jsyk/PIP-Watch/doc/gde021a1_framebuffer.png

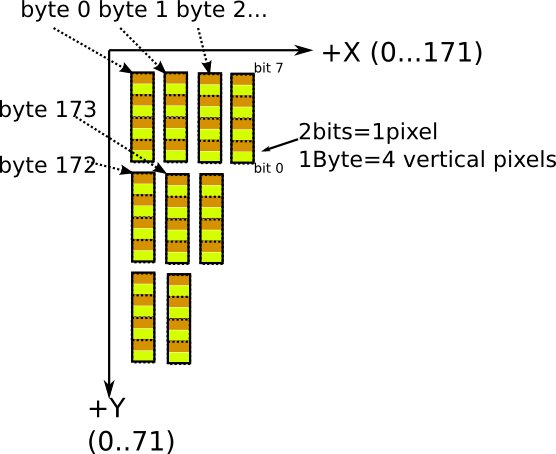
doc/gde021a1_framebuffer.png
