jsyk/PIP-Watch/doc/swarch-whitebg.png

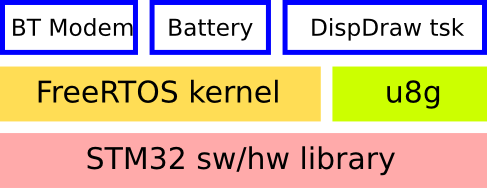
doc/swarch-whitebg.png
