jsyk/PIP-Watch/epd_driver_basic_stm32f101_sw/cube/stm32f101c8t6.jpg

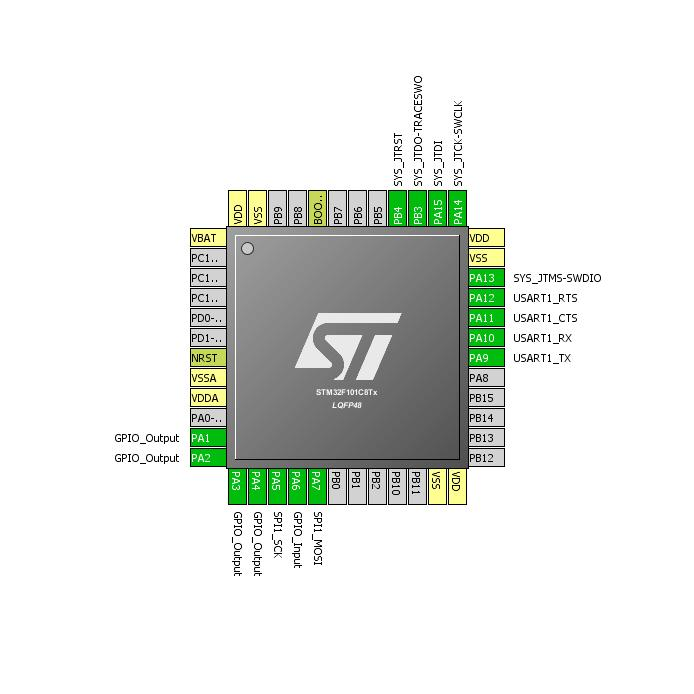
epd_driver_basic_stm32f101_sw/cube/stm32f101c8t6.jpg
