jsyk/PIP-Watch/pipwatch_zero-fw/stm_epd_connection.png

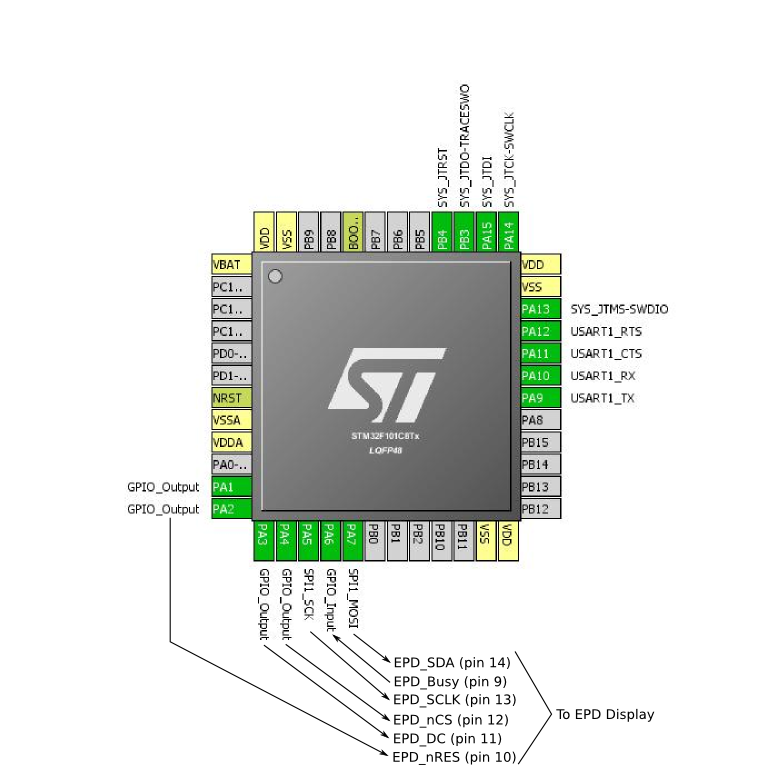
pipwatch_zero-fw/stm_epd_connection.png
