jsyk/PIP-Watch/epd_driver_basic_stm32f101_sw/cube/stm32f101c8t6.ioc

Mcu.UserName=STM32F101C8Tx
PA1.Signal=GPIO_Output
PA10.Signal=USART1_RX
PA11.Signal=USART1_CTS
PA12.Signal=USART1_RTS
PA13.Signal=SYS_JTMS-SWDIO
PA14.Signal=SYS_JTCK-SWCLK
PA15.Signal=SYS_JTDI
PA2.Signal=GPIO_Output
PA3.Signal=GPIO_Output
PA4.Signal=GPIO_Output
PA5.Signal=SPI1_SCK
PA6.Signal=GPIO_Input
PA7.Signal=SPI1_MOSI
PA9.Signal=USART1_TX
PB3.Signal=SYS_JTDO-TRACESWO
PB4.Signal=SYS_JTRST
