jsyk/PIP-Watch/pipwatch_zero-fw/btm.c

#include "btm.h"
#include "main.h"
#include "utils.h"
#include "leds.h"
#include "motor.h"
#include "gui.h"
#include "streamlnk.h"

#include <string.h>
#include <ctype.h>

/* Scheduler includes. */
// #include "FreeRTOS.h"
#include "task.h"
// #include "queue.h"
#include "STM32_USART.h"

/* Library includes. */
#include "stm32f10x_it.h"


/* the state of the bluetooth modem */
int btm_state = BTMST_NonConfigured;



/* Remove all characters already received in USART queue */
void usartDrainInput(long lPort)
{
    int ch;
    while (xSerialGetChar(lPort, &ch, 0) == pdPASS)
        ;
}


/* Receive all characters until the buffer is full or there are none more
 * within the timeout */
int usartGetString(long lPort, char *buf, int buflen, TickType_t xBlockTime)
{
    int ch;            /* current character */
    int cnt = 0;        /* number of chars received */

    while (cnt < (buflen-1)) {
        if (xSerialGetChar(lPort, &ch, xBlockTime) != pdPASS) {
            /* no more chars in the buffer and we waited a timeout -> bail out */
            break;
        }

        /* save the character into buffer */
        buf[cnt++] = ch;
    }

    /* null-terminate, if possible */
    if (cnt < buflen) {
        buf[cnt] = 0;
    }

    /* print the received string to display */
    printstr(buf);

    return cnt;
}

/* Receive characters until the buffer is full or end of line or there are none more
 * within the timeout. */
int usartGetLine(long lPort, char *buf, int buflen, TickType_t xBlockTime)
{
    int ch;            /* current character */
    int cnt = 0;        /* number of chars received */
    int expect_newline = 0;

    while (cnt < (buflen-1)) {
        if (xSerialPeekChar(lPort, &ch, xBlockTime) != pdPASS) {
            /* no more chars in the buffer and we waited a timeout -> bail out */
            break;
        }

        if (expect_newline && ch != '\n') {
            /* we were expecting \n now, but it has not come -> leave ch in the queue and exit */
            break;
        }

        /* save the character into buffer */
        buf[cnt++] = ch;

        /* if it is \r, then expect \n as the next character */
        if (ch == '\r') {
            expect_newline = 1;
        }

        /* physically remove the character we've peeked from the queue */
        xSerialGetChar(lPort, &ch, xBlockTime);

        if (ch == '\n') {
            /* end of line -> end of str, for now */
            break;
        }
    }

    /* null-terminate, if possible */
    if (cnt < buflen) {
        buf[cnt] = 0;
    }

    /* print the received string to display */
    // printstr(buf);

    return cnt;
}


/* Expecting the 'OK' response from modem. Wait for it and do anything
 * possible to decode it. */
int btmExpectOK()
{
    const int buflen = 64;
    char xbuf[buflen];
    int len;

    len = usartGetString(comBTM, xbuf, buflen, ( TickType_t ) 200 / portTICK_PERIOD_MS);

    char *buf = xbuf;

    if (len < 4) {
        goto err;
    }

    if ((buf[0] == 'A' && buf[1] == 'T') || (buf[0] == '\r')) {
        // discard echo text
        while (!(buf[0] == '\r' && buf[1] == '\n')) {
            if (buf[0] == 0) {
                goto err;
            }
            ++buf;
        }
        // skip \r\n
        buf += 2;
    }

    if (buf[0] != 'O') {
        goto err;
    }
    if (buf[1] != 'K') {
        goto err;
    }
    if (buf[2] != '\r') {
        goto err;
    }
    if (buf[3] != '\n') {
        goto err;
    }

    return 0;

err:
#if 0
    zbuf = pvPortMalloc(sizeof(char) * 64);
    strncpy(zbuf, xbuf, len);
    for (int i = 0; i < 63; ++i) {
        if (zbuf[i] == '\r' || zbuf[i] == '\n') {
            zbuf[i] = ' ';
        }
    }
    zbuf[63] = 0;
    xQueueSend(toDisplayStrQueue, &zbuf, 0);
#endif
    return 1;
}

void setBtmState(int new_btmst)
{
    btm_state = new_btmst;

    switch (btm_state) {
        case BTMST_NonConfigured:
            LEDs_Set(LED0, LED_INTENS_100, LED_INTENS_0, LED_INTENS_0);
            break;

        case BTMST_Configured:
            LEDs_Set(LED0, LED_INTENS_100, LED_INTENS_100, LED_INTENS_0);
            break;

        case BTMST_Listening:
            LEDs_Set(LED0, LED_INTENS_0, LED_INTENS_100, LED_INTENS_0);
            break;

        case BTMST_Connected:
            LEDs_Set(LED0, LED_INTENS_0, LED_INTENS_0, LED_INTENS_100);
            break;

        default: break;
    }
}


void btmInitModem()
{
    /* Initialise COM0, which is USART1 according to the STM32 libraries. */
    lCOMPortInit( comBTM, mainBAUD_RATE );

    setBtmState(BTMST_NonConfigured);

    /* Reset BTM */
    #if 0
    GPIO_ResetBits(BTM_Reset_Port, BTM_Reset_Pin);
    vTaskDelay( ( TickType_t ) 10 / portTICK_PERIOD_MS );
    GPIO_SetBits(BTM_Reset_Port, BTM_Reset_Pin);
    #endif

    // do { } while (1);

    // const char *atEscape = "^^^";
    const char *atEscapeChar = "^";
    const char *atEOL = "\r";
    const char *atTest = "AT\r";
    
    // after-reset condition: give the BT module some time to init itself.
    vTaskDelay( ( TickType_t ) 1000 / portTICK_PERIOD_MS );

    /* Reset */
    const char *atReset = "ATZ\r";
    lSerialPutString( comBTM, atReset, strlen(atReset) );
    if (btmExpectOK()) {
        // failed; Try getting into command mode by sending the escape sequence:
        do {
            // Before the escape sequence there must be silence for guard time
            vTaskDelay( ( TickType_t ) 120 / portTICK_PERIOD_MS );
            
            lSerialPutString( comBTM, atEscapeChar, strlen(atEscapeChar) );
            vTaskDelay( ( TickType_t ) 120 / portTICK_PERIOD_MS );
            lSerialPutString( comBTM, atEscapeChar, strlen(atEscapeChar) );
            vTaskDelay( ( TickType_t ) 120 / portTICK_PERIOD_MS );
            lSerialPutString( comBTM, atEscapeChar, strlen(atEscapeChar) );
            
            // After the escape sequence there must be silence for guard time
            vTaskDelay( ( TickType_t ) 120 / portTICK_PERIOD_MS );

            // Send end of line
            lSerialPutString( comBTM, atEOL, strlen(atEOL) );
            // wait a little bit
            vTaskDelay( ( TickType_t ) 100 / portTICK_PERIOD_MS );
            // empty input buffer
            usartDrainInput(comBTM);            /* this drains possible 'ERROR 05' status */
            
            // Send plain AT
            lSerialPutString( comBTM, atTest, strlen(atTest) );
            
            // expect "OK\r\n"
        } while (btmExpectOK());
    }


    setBtmState(BTMST_Configured);

#if 0    
    GPIO_InitTypeDef GPIO_InitStruct;
    GPIO_InitStruct.GPIO_Pin = GPIO_Pin_2 /*| GPIO_Pin_1*/;
    GPIO_InitStruct.GPIO_Speed = GPIO_Speed_2MHz;
    GPIO_InitStruct.GPIO_Mode = GPIO_Mode_IN_FLOATING;
    GPIO_Init( GPIOA, &GPIO_InitStruct );
#endif
#if 0
    /* Set mode */
    const char *atModeF1 = "AT&F1\r";
    lSerialPutString( comBTM, atModeF1, strlen(atModeF1) );
    if (btmExpectOK()) {
        // failed
        assert_failed(__FILE__, __LINE__);
    }
#endif

    /* Set Friendly name */
    const char *atSetDeviceName = "AT+BTF=\"PIP-Watch\"\r";
    lSerialPutString( comBTM, atSetDeviceName, strlen(atSetDeviceName) );
    if (btmExpectOK()) {
        // failed
        vTaskDelay( portMAX_DELAY );
        assert_failed(__FILE__, __LINE__);
    }

#if 0
    /* Open and make unit detectable */
    const char *atEnaRadio2 = "AT+BTO\r";
    lSerialPutString( comBTM, atEnaRadio2, strlen(atEnaRadio2) );
    if (btmExpectOK()) {
        // failed
        assert_failed(__FILE__, __LINE__);
    }
#endif

    /* Set passkey */
    const char *atSetPin = "AT+BTK=\"1984\"\r";
    lSerialPutString( comBTM, atSetPin, strlen(atSetPin) );
    if (btmExpectOK()) {
        // failed
        assert_failed(__FILE__, __LINE__);
    }

#if 1
    /* Set mode F1: Minimal power consumption, 9600Bd; mode F1= 0:4,4,48,80(50ms)
        S508 = 2500 = page scan interval [ms]
        S509 = 11 = page scan window [ms]
    */
    const char *atSetMinPower = "AT&F1\r";          
    // const char *atSetMinPower = "AT&F0\r";          // Medium power consumption, 9600Bd
    lSerialPutString( comBTM, atSetMinPower, strlen(atSetMinPower) );
    if (btmExpectOK()) {
        // failed
        assert_failed(__FILE__, __LINE__);
    }

#if 1
    /* Set shorter Page scan interval: 1200ms, lower latency when opening the connection, higher
     * probability of success, higher avg power.  */
    // const char *atSniffStatus = "ATI13\r";
    // const char *atSniffMaxInterval = "ATS564=60\r";
    const char *atPgScanInterv = "ATS508=1200\r";
    lSerialPutString( comBTM, atPgScanInterv, strlen(atPgScanInterv) );
    if (btmExpectOK()) {
        // failed
        assert_failed(__FILE__, __LINE__);
    }
#endif
#endif

#if 0
    /* Make modem Discoverable and connectable */
    const char *atEnaRadio = "AT+BTP\r";
    lSerialPutString( comBTM, atEnaRadio, strlen(atEnaRadio) );
    if (btmExpectOK()) {
        // failed
        assert_failed(__FILE__, __LINE__);
    }

    /* auto-save pairing info */
    const char *atSavePairing = "ATS538=1\r";
    lSerialPutString( comBTM, atSavePairing, strlen(atSavePairing) );
    if (btmExpectOK()) {
        // failed
        assert_failed(__FILE__, __LINE__);
    }
    
#else
    /* Make modem Connectable (Enable page scans only) */
    const char *atEnaRadio = "AT+BTG\r";
    // const char *atEnaRadio = "AT+BTG10BF48CD0778\r";         /* no effect on power consumption */
    lSerialPutString( comBTM, atEnaRadio, strlen(atEnaRadio) );
    if (btmExpectOK()) {
        // failed
        assert_failed(__FILE__, __LINE__);
    }
#endif

#if 0
    /* Query Sniff state */
    // const char *atSniffStatus = "ATI13\r";           // mode F1= 0:4,4,48,80
    const char *atSniffStatus = "ATS509?\r";
    lSerialPutString( comBTM, atSniffStatus, strlen(atSniffStatus) );
    /* btmExpectOK() WILL fail here! */
    if (btmExpectOK()) {
        // failed
        assert_failed(__FILE__, __LINE__);
    }
#endif

#if 1
    /* Disable local echo */
    const char *atDisableEcho = "ATE0\r";
    lSerialPutString( comBTM, atDisableEcho, strlen(atDisableEcho) );
    if (btmExpectOK()) {
        // failed
        vTaskDelay( portMAX_DELAY );
        assert_failed(__FILE__, __LINE__);
    }
#endif

    setBtmState(BTMST_Listening);
}


/* Described at the top of this file. */
void BluetoothModemTask( void *pvParameters )
{
    /* Just to avoid compiler warnings. */
    ( void ) pvParameters;

    /* modem setup  */
    btmInitModem();

    while (1) {
        btm_rx_stream(comBTM);
    }
}




/* Decode (unsolicitated) modem message.
 * Return 0 is parser should continue, 1 to reset parser into init state. */
/* Decode and act on status message received from the modem. 
 * The status text is normally ended by <lf> and \0.

RING <btaddr><lf>
PIN? <btaddr><lf>
PAIR <n> <btaddr><lf>
PAIR 0 <btaddr> <MM><lf>
RX<string><lf>
CONNECT <btaddr><lf>
NO CARRIER<lf>

 */
int do_decode_btm_status(const char *buf)
{
    if (strncmp(buf, "RING ", 5) == 0) {
        /* Incomming connection -> send an ack to accept */
        const char *atAcceptRing = "ATA\r";
        lSerialPutString( comBTM, atAcceptRing, strlen(atAcceptRing) );
    
        setBtmState(BTMST_Connected);
        Motor_Pulse(MOTOR_DUR_LONG);
        
        return 1;
    }

    if (strncmp(buf, "CONNECT ", 8) == 0) {
        /* Connected to a remote. */
        /* no need to do anything else now */
        return 1;
    }

    if (strncmp(buf, "NO CARRIER", 10) == 0) {
        /* Disconnect */
        setBtmState(BTMST_Listening);
        return 1;
    }

    return 1;
}
