jsyk/PIP-Watch/pipwatch_zero-fw/btm.h

#ifndef BTM_H
#define BTM_H

/* COM port and baud rate used by the echo task. */
#define comBTM                                 ( 1 )
#define mainBAUD_RATE                       ( 9600 )

/* PC4 = Reset */
#define BTM_Reset_Port              GPIOC
#define BTM_Reset_Pin               GPIO_Pin_4


#define BTMST_NonConfigured         0
#define BTMST_Configured            1
#define BTMST_Listening             2
#define BTMST_Connected             3


void BluetoothModemTask( void *pvParameters );

/* Decode (unsolicitated) modem message.
 * Return 0 is parser should continue, 1 to reset parser into init state. */
int do_decode_btm_status(const char *buf);

#endif
